mfoster0/RiverWaterQuality/Media/CustomResistor.png

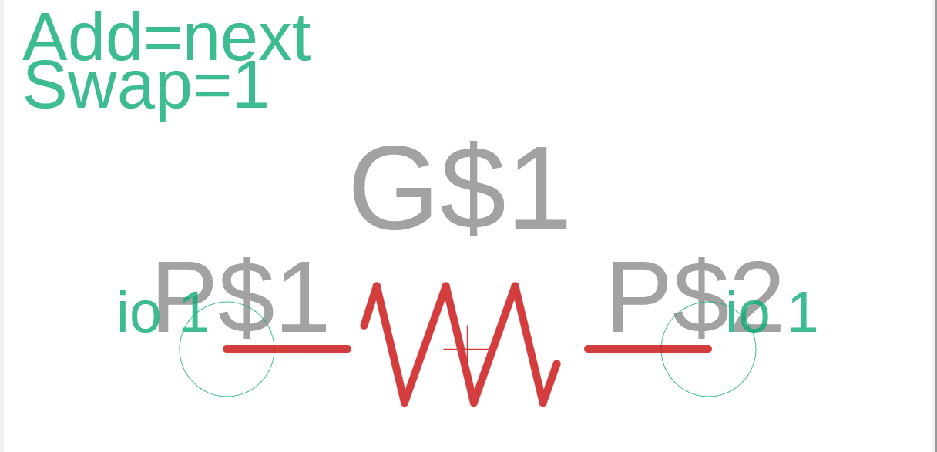
Media/CustomResistor.png
