mfoster0/RiverWaterQuality/Media/DeploymentSites.png

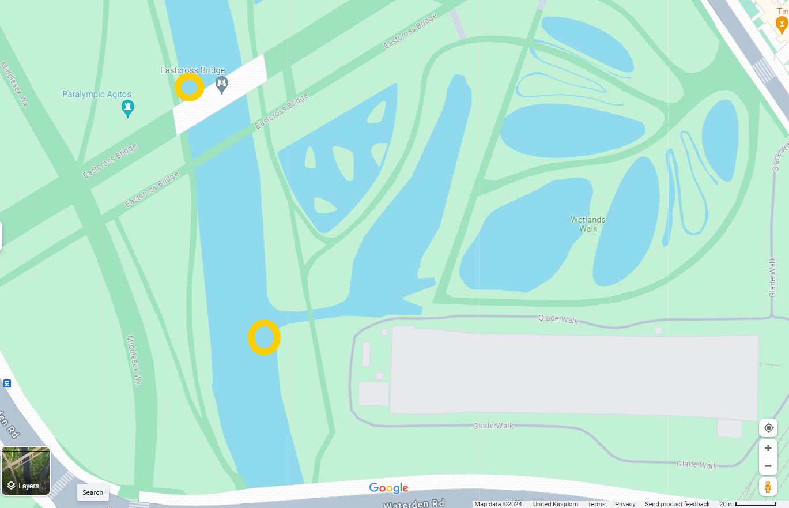
Media/DeploymentSites.png
