mfoster0/RiverWaterQuality/Media/EastcrossBridgeOutfall1.jpg

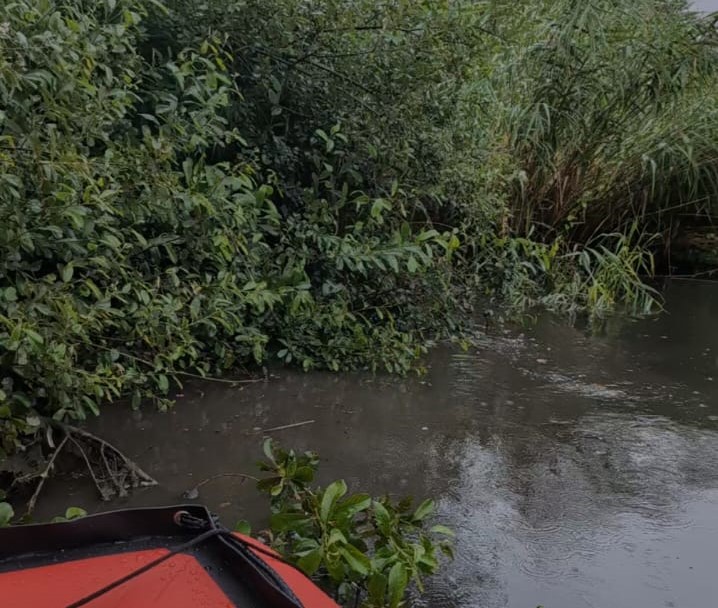
Media/EastcrossBridgeOutfall1.jpg
