mfoster0/RiverWaterQuality/Media/EastcrossBridgeOutfall2.jpg

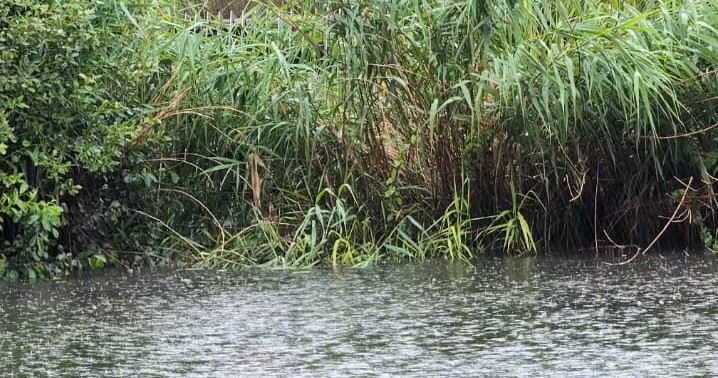
Media/EastcrossBridgeOutfall2.jpg
