mfoster0/RiverWaterQuality/Media/Exhibit.jpg

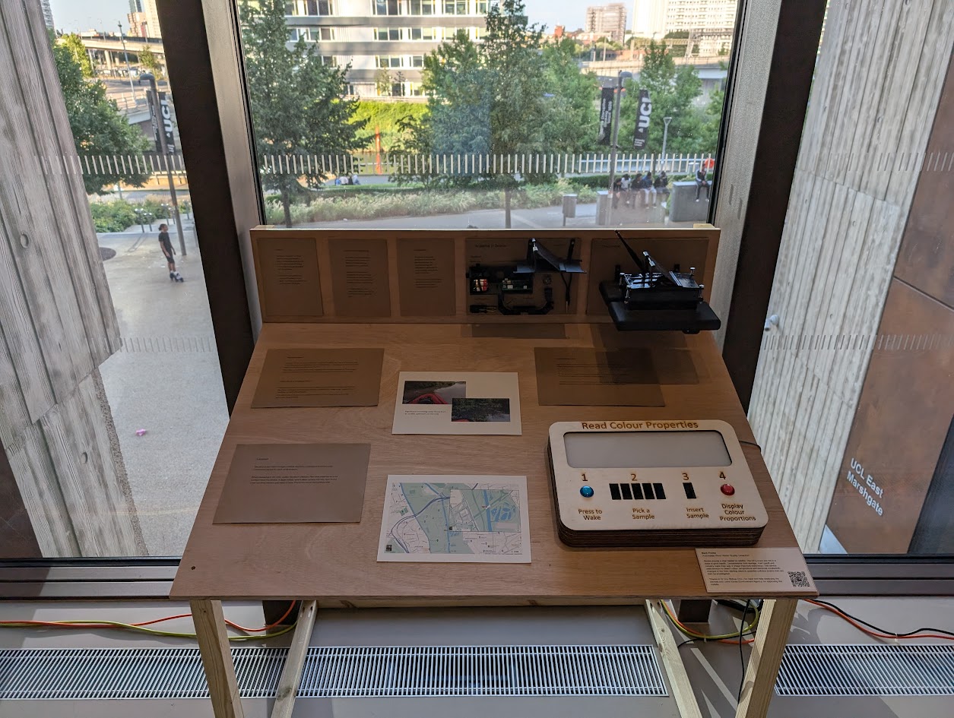
Media/Exhibit.jpg
