mfoster0/RiverWaterQuality/Media/ExhibitDevice.jpg

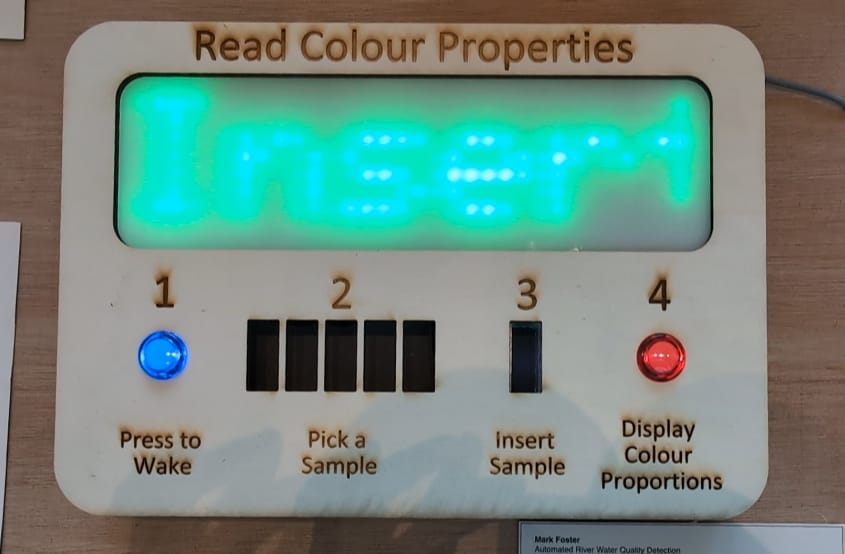
Media/ExhibitDevice.jpg
