mfoster0/RiverWaterQuality/Media/ExhibitDeviceCircuitSketch.jpg

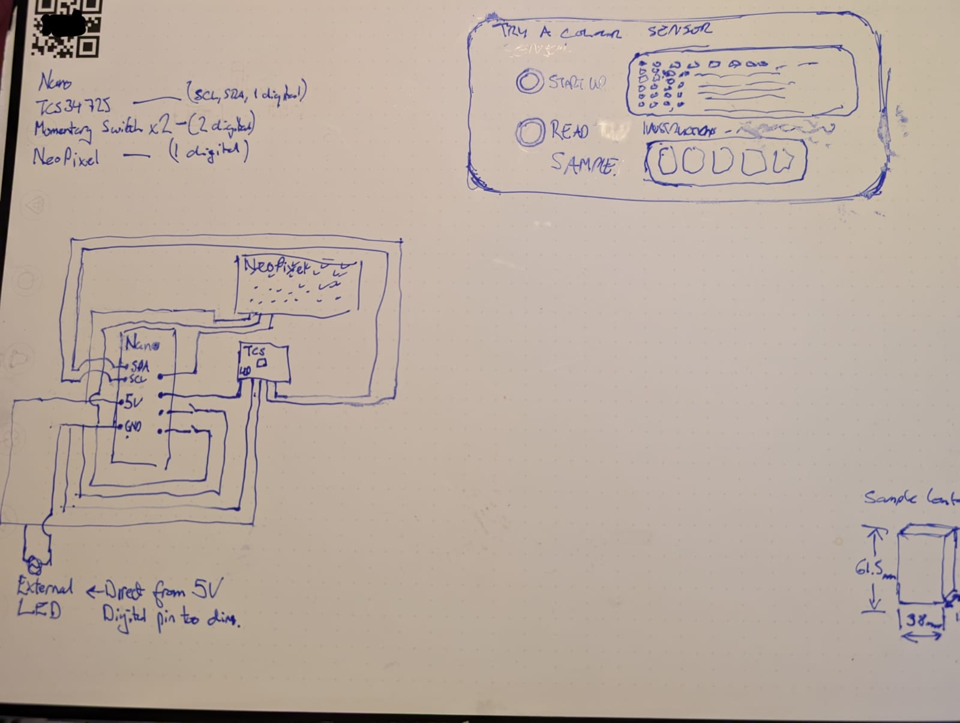
Media/ExhibitDeviceCircuitSketch.jpg
