mfoster0/RiverWaterQuality/Media/GY-33.jpg

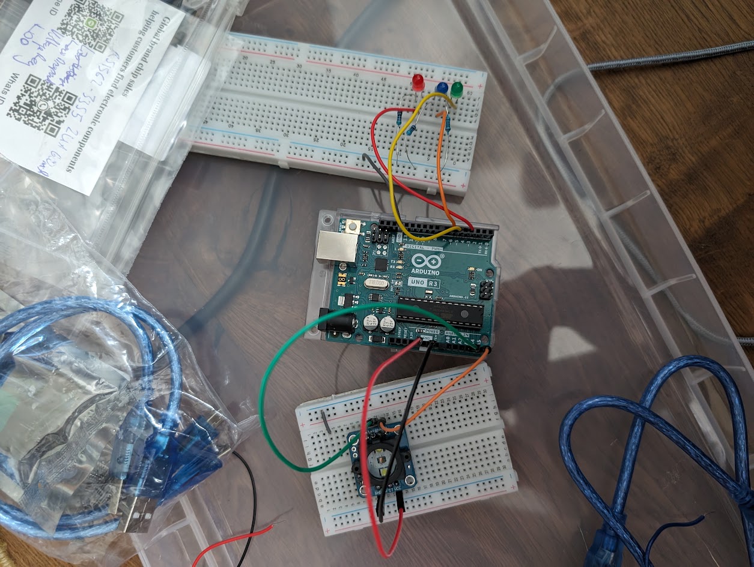
Media/GY-33.jpg
