mfoster0/RiverWaterQuality/Media/NeopreneCustomSeal.jpg

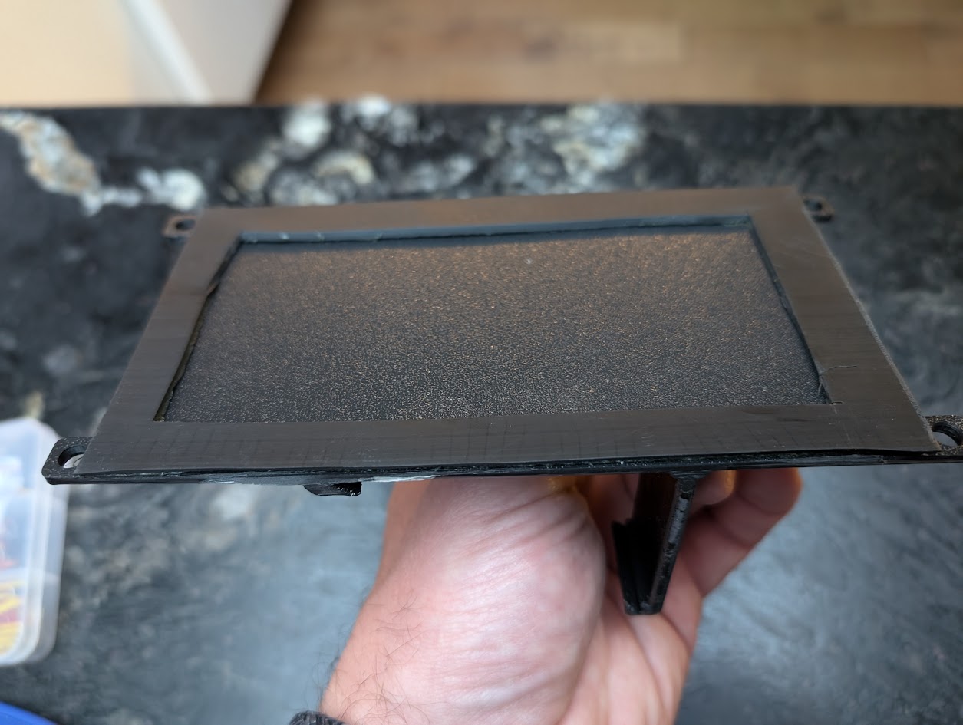
Media/NeopreneCustomSeal.jpg
