mfoster0/RiverWaterQuality/Media/OutfallDump3.jpg

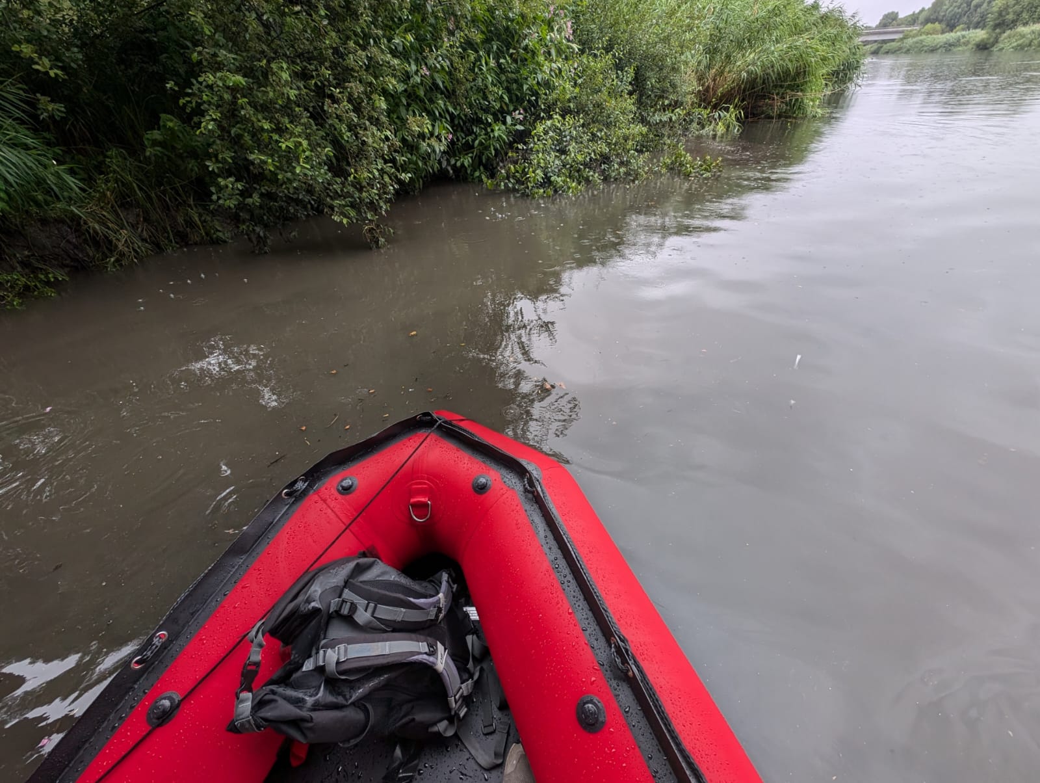
Media/OutfallDump3.jpg
