mfoster0/RiverWaterQuality/Media/Proto3Deploy.jpg

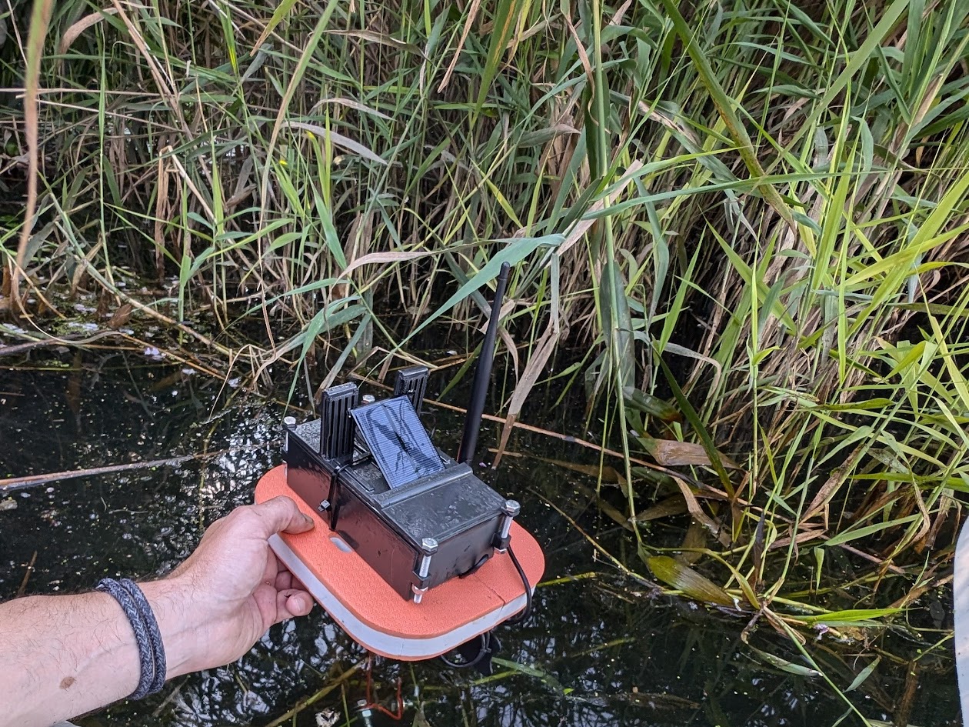
Media/Proto3Deploy.jpg
