mfoster0/RiverWaterQuality/Media/Proto3Far.jpg

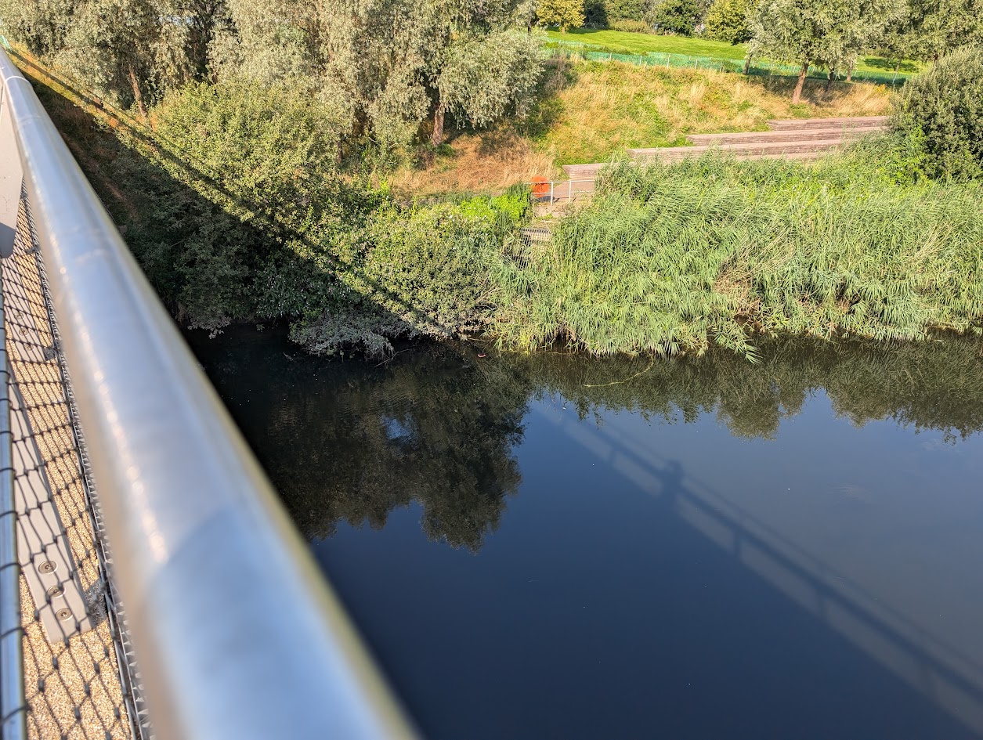
Media/Proto3Far.jpg
