mfoster0/RiverWaterQuality/Media/Proto3Seal.jpg

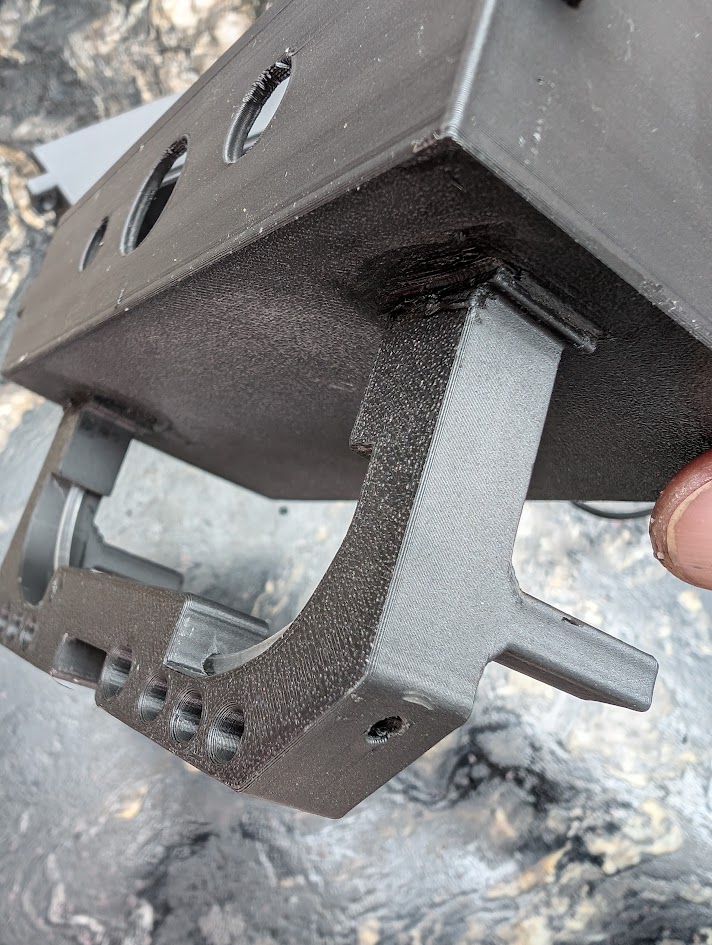
Media/Proto3Seal.jpg
