mfoster0/RiverWaterQuality/Media/WhatsApp Image 2024-08-18 at 07.57.30_258b90e4.jpg

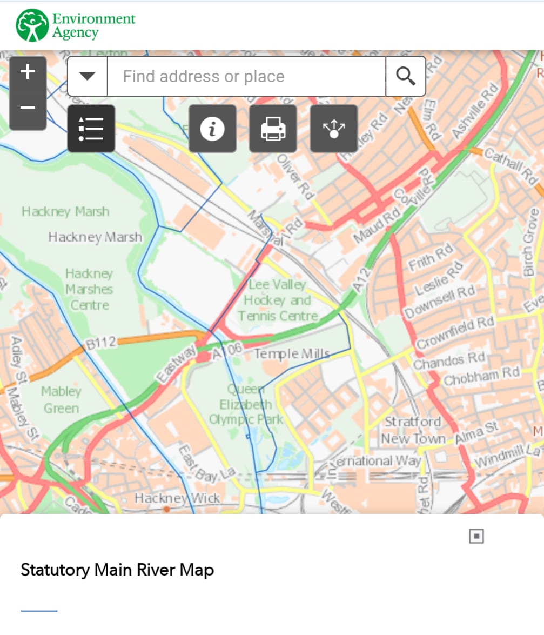
Media/WhatsApp Image 2024-08-18 at 07.57.30_258b90e4.jpg
