mfoster0/RiverWaterQuality/FusionFiles/Device/PreviousVersions/OpticalFibreHolderShortenedNoFloatHolder v3.stl

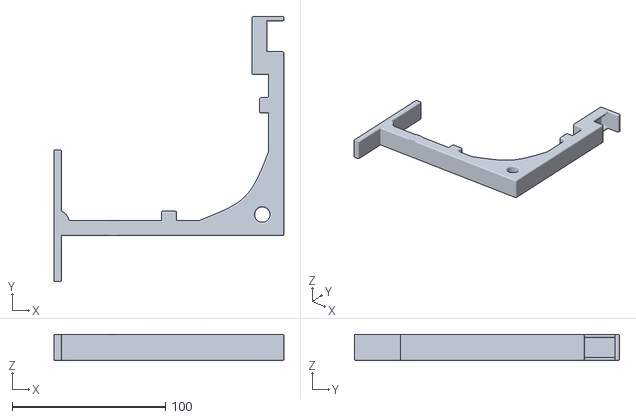
[picture p50: CAD file, 2024-08-18, an earlier design]
FusionFiles/Device/PreviousVersions/OpticalFibreHolderShortenedNoFloatHolder v3.stl
150.0 x 173.0 x 17.0
