mfoster0/RiverWaterQuality/FusionFiles/Device/PreviousVersions/StackableFloat v1.stl

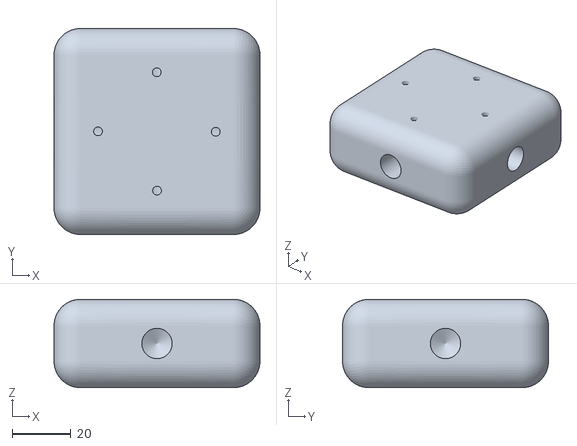
[picture p51: CAD file, 2024-08-18, an earlier design]
FusionFiles/Device/PreviousVersions/StackableFloat v1.stl
70.0 x 70.0 x 30.0
