mfoster0/RiverWaterQuality/FusionFiles/Device/PreviousVersions/FloatP2 v2.stl

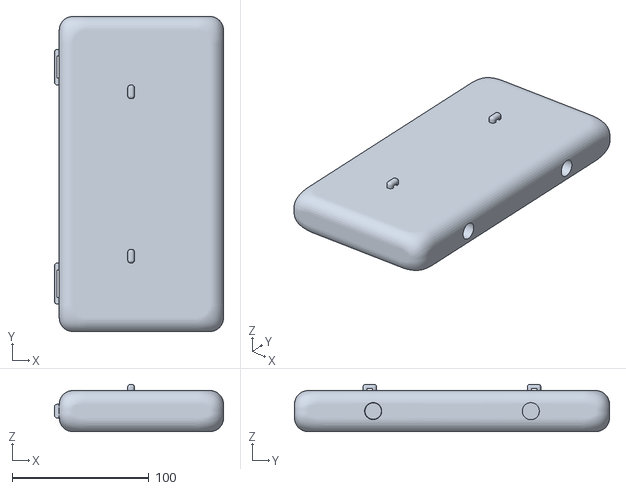
[picture p52: CAD file, 2024-08-18, an earlier design]
FusionFiles/Device/PreviousVersions/FloatP2 v2.stl
123.5 x 230.0 x 34.5
