mfoster0/RiverWaterQuality/FusionFiles/Device/PreviousVersions/Rudder v1.stl

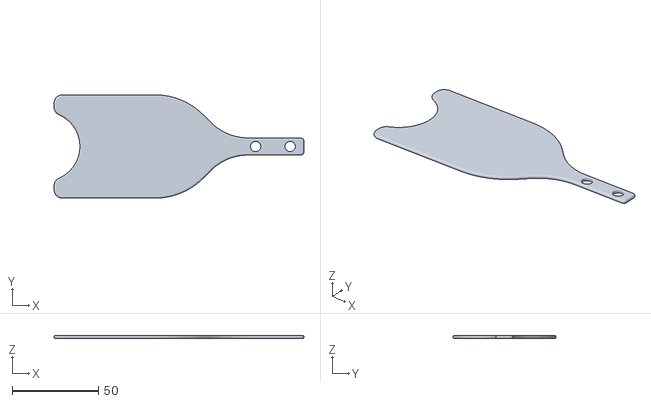
[picture p53: CAD file, 2024-08-18, an earlier design]
FusionFiles/Device/PreviousVersions/Rudder v1.stl
145.0 x 60.0 x 2.00
