mfoster0/RiverWaterQuality/Media/ExhibitInstall.jpg

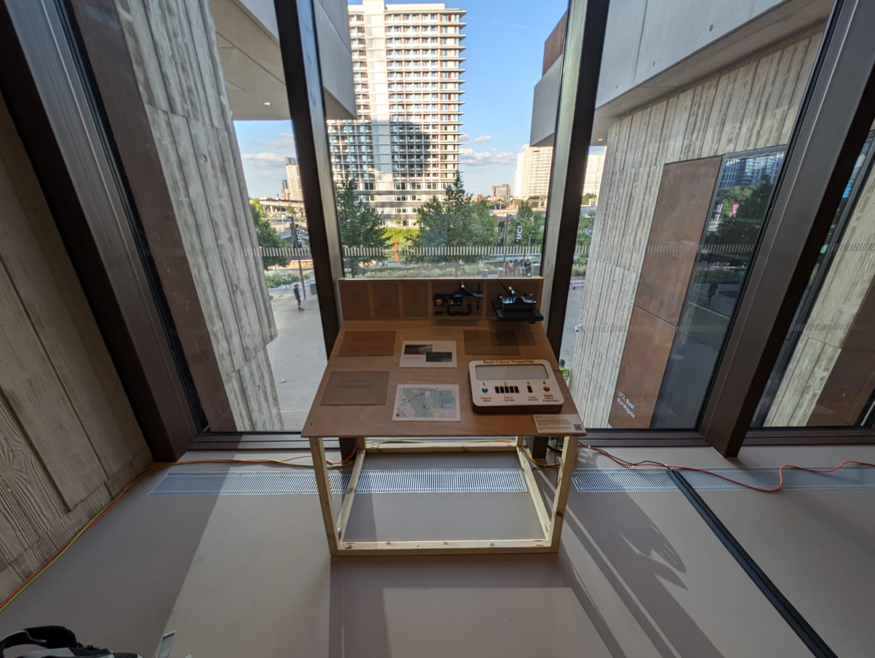
Media/ExhibitInstall.jpg
