mfoster0/RiverWaterQuality/Media/Proto3Fix2.jpg

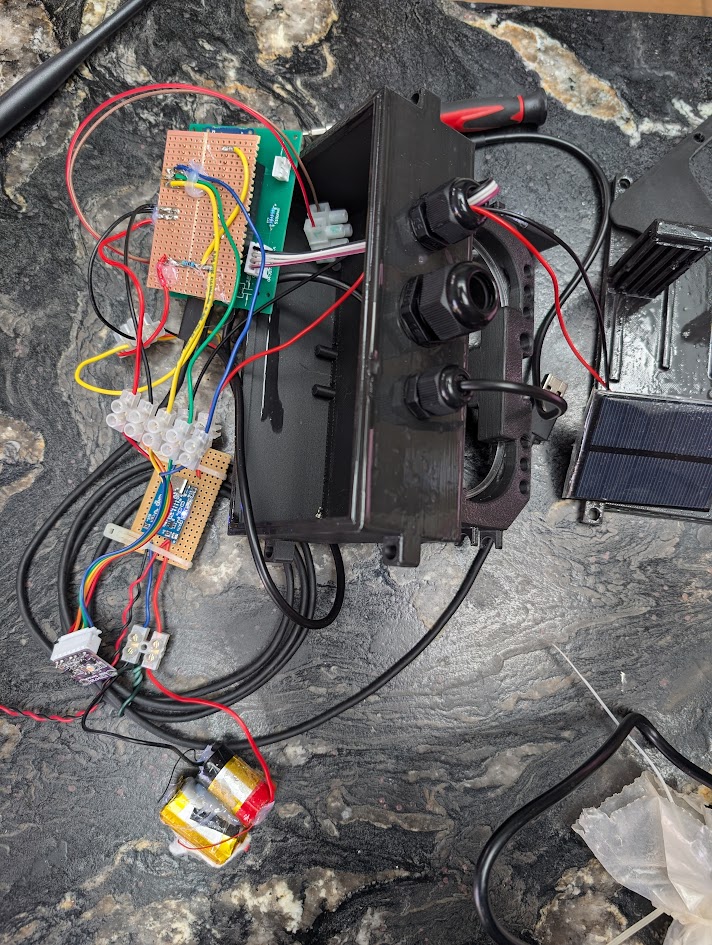
Media/Proto3Fix2.jpg
