mfoster0/RiverWaterQuality/Media/Proto3Fix.jpg

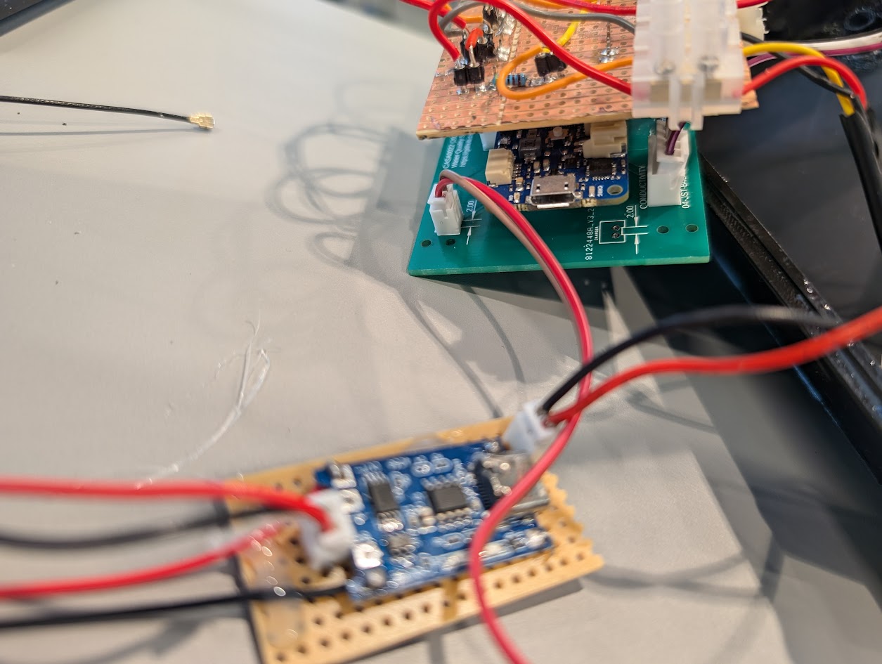
Media/Proto3Fix.jpg
